emmanuelponsone/Swim_Timing/03 - Electronic Design/altium/Placa madre/Bottom layer.pdf

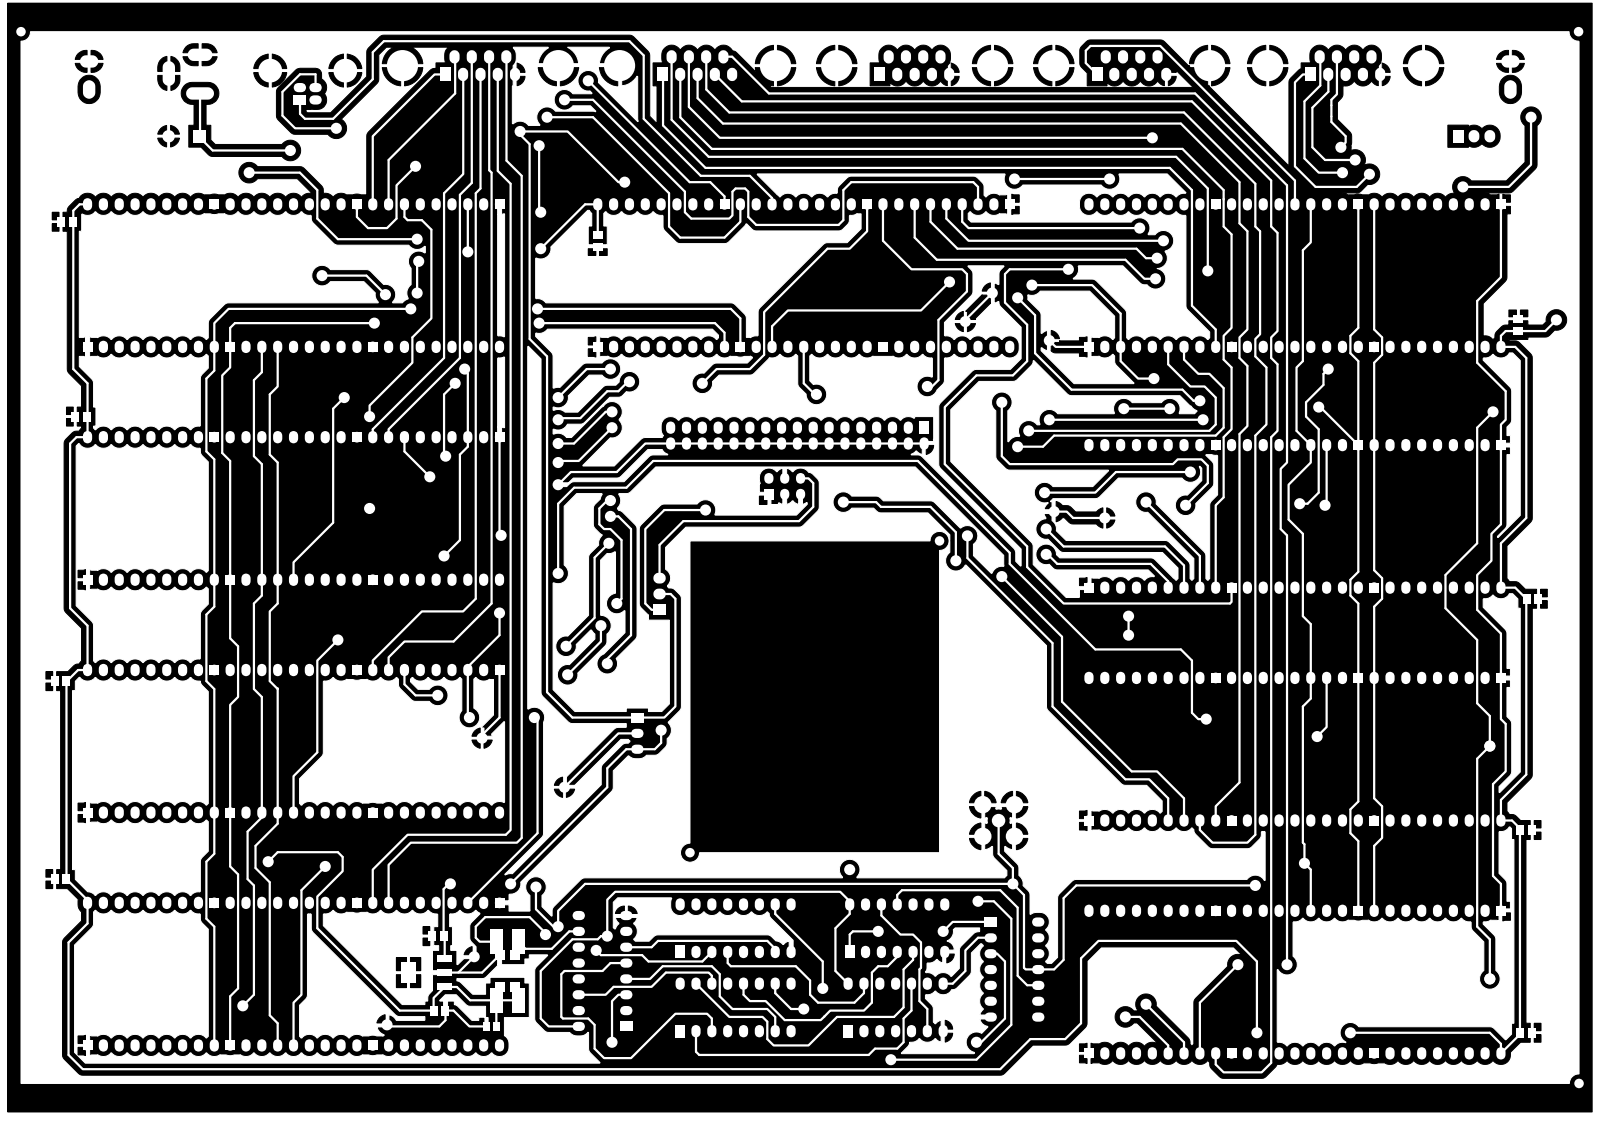
[picture p93: page 1]
