emmanuelponsone/Swim_Timing/03 - Electronic Design/altium/Placa madre/TOP LAYER.pdf

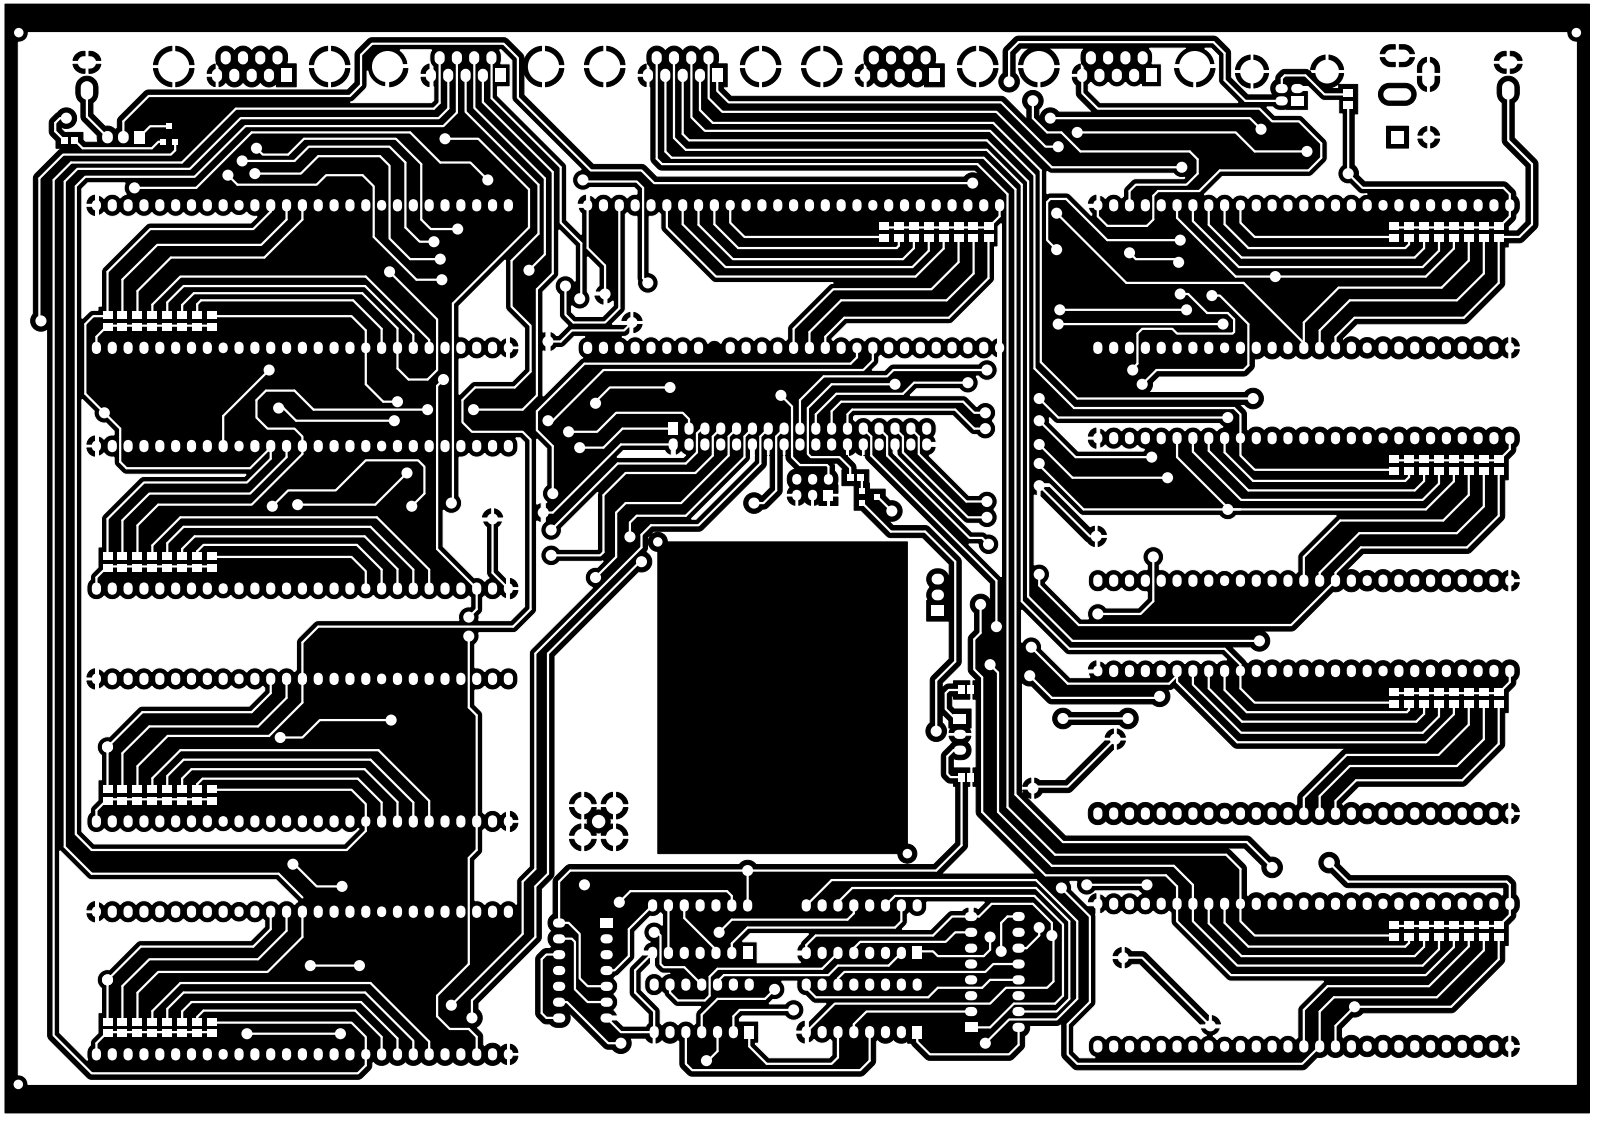
[picture p94: page 1]
