emmanuelponsone/Swim_Timing/03 - Electronic Design/altium/Placa madre 2.0/filminas y nc drill/Bottom layer.pdf

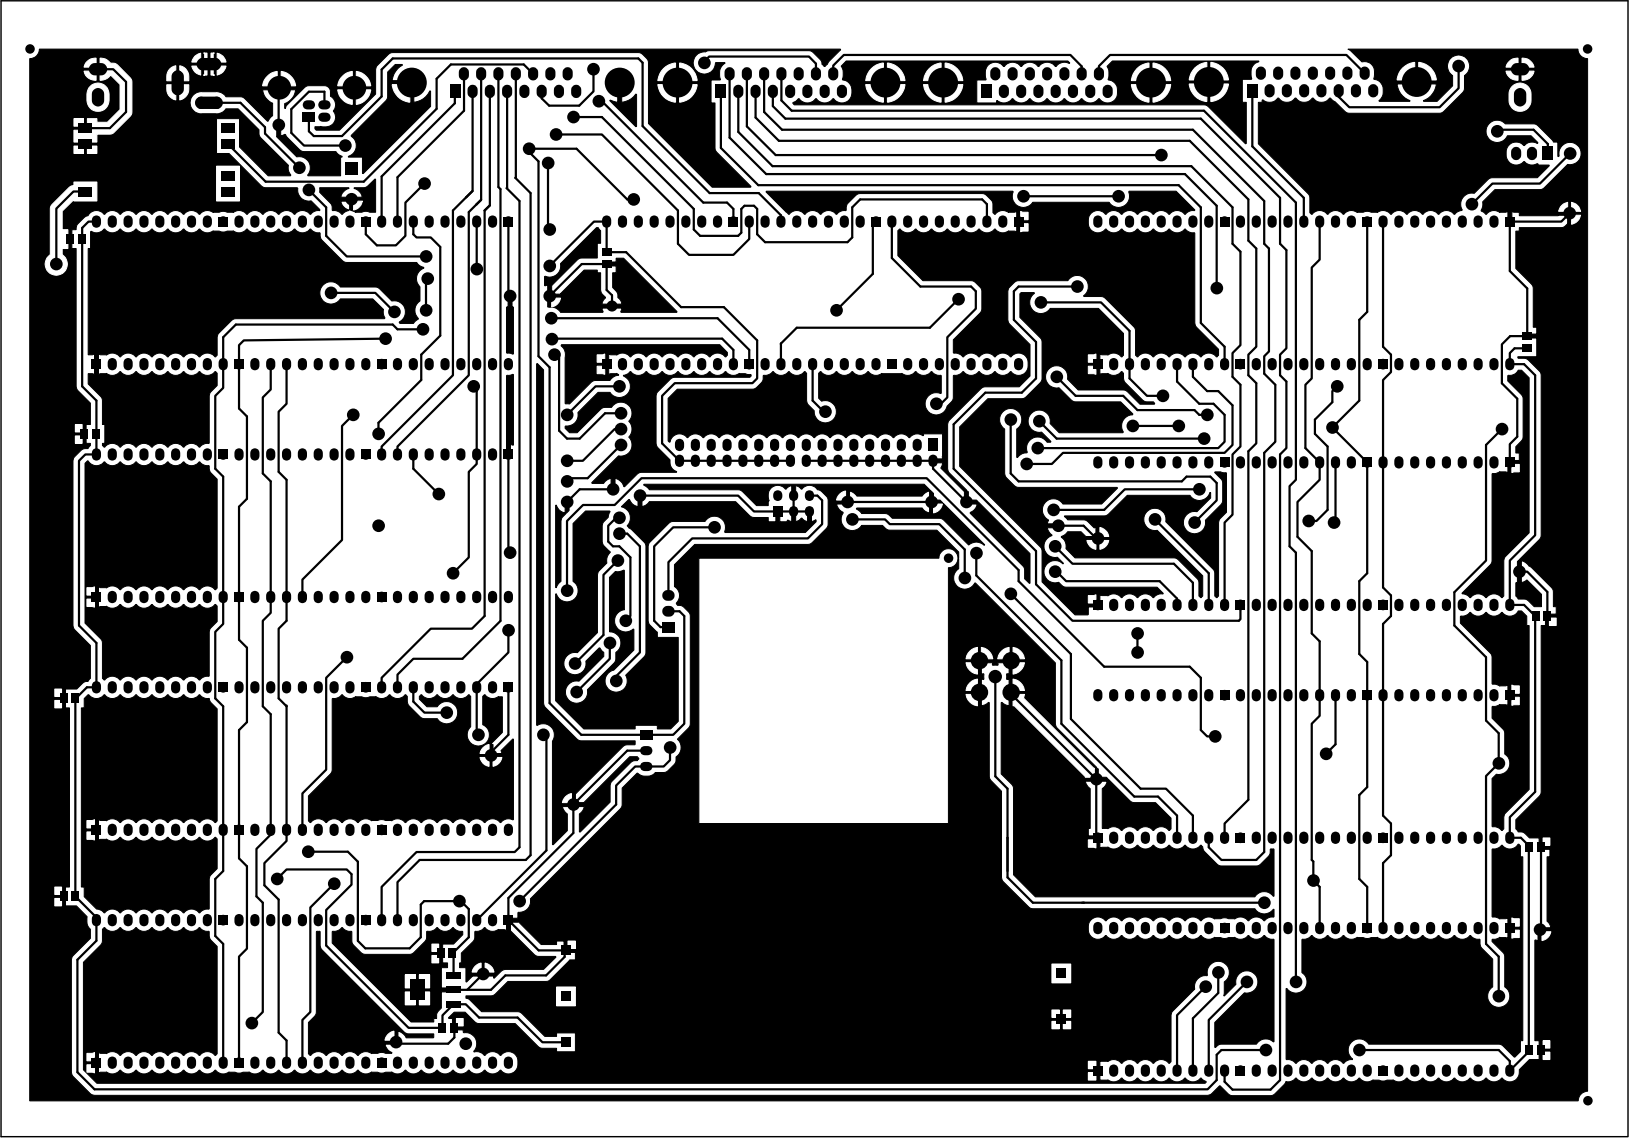
[picture p95: page 1]
