emmanuelponsone/Swim_Timing/03 - Electronic Design/altium/Placa madre 2.0/filminas y nc drill/TOP LAYER.pdf

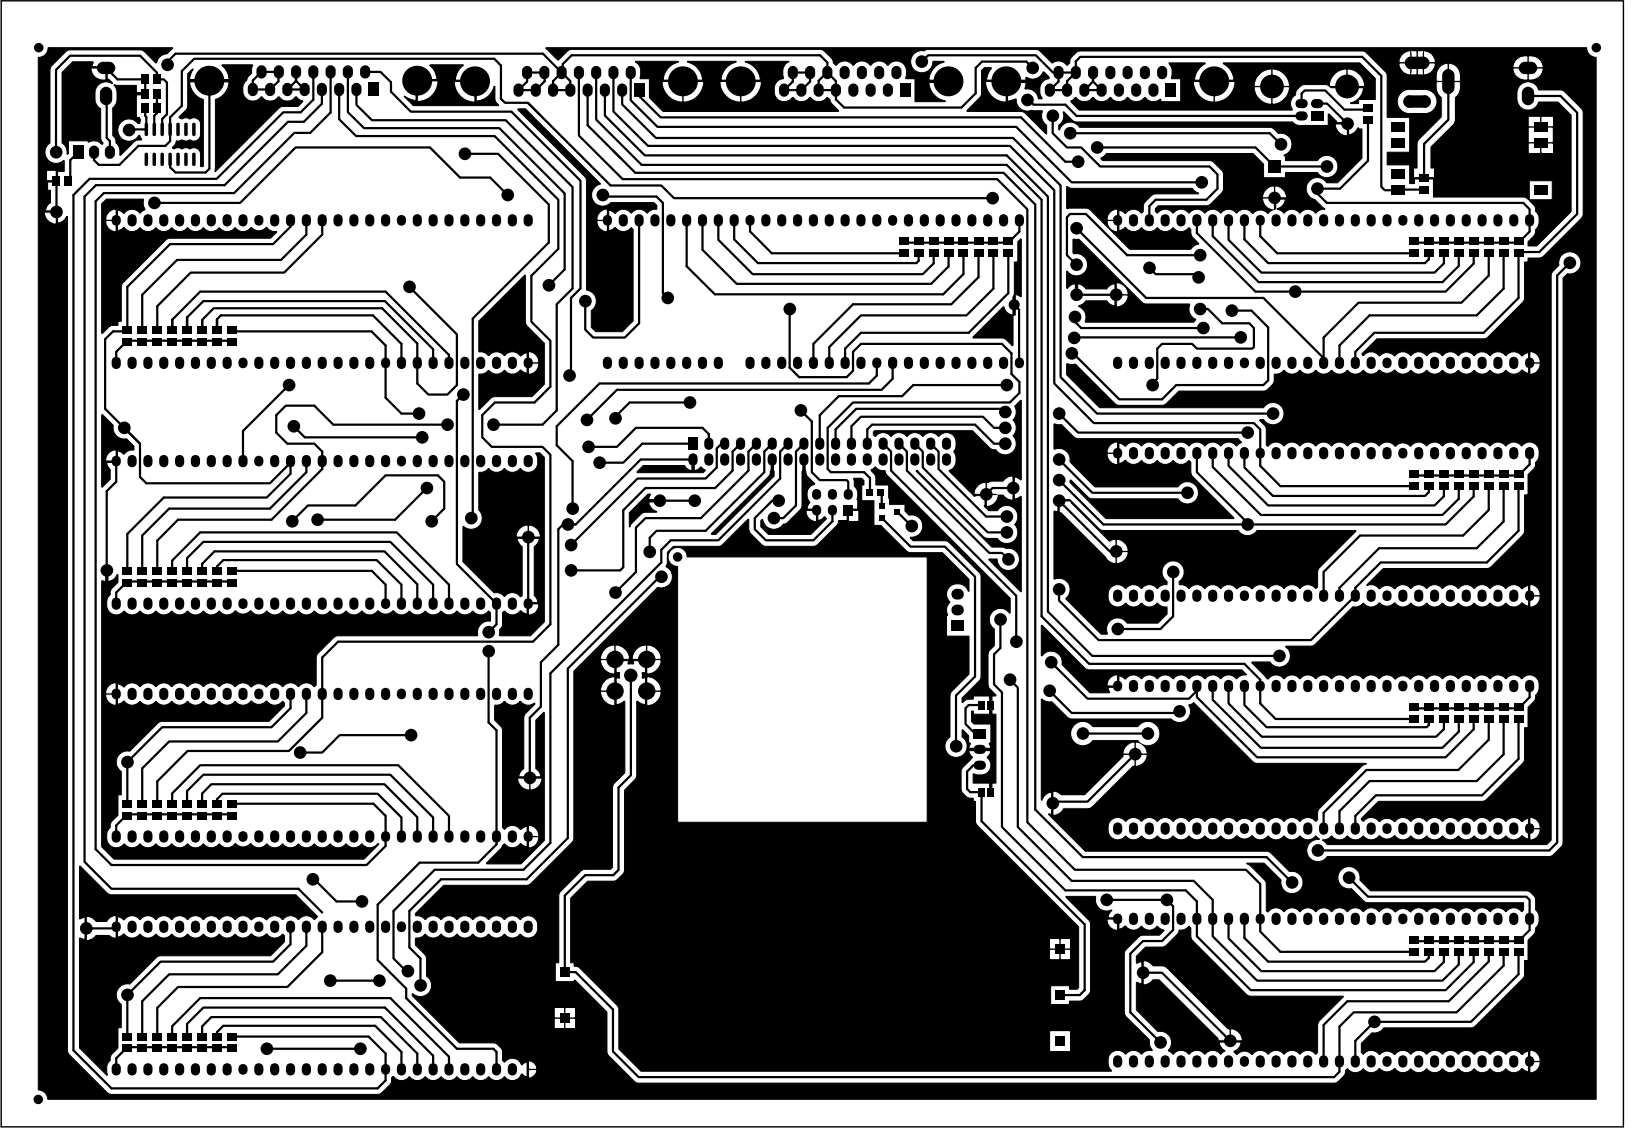
[picture p96: page 1]
