emmanuelponsone/Swim_Timing/03 - Electronic Design/altium/Placa madre/filminas/bottom layer.pdf

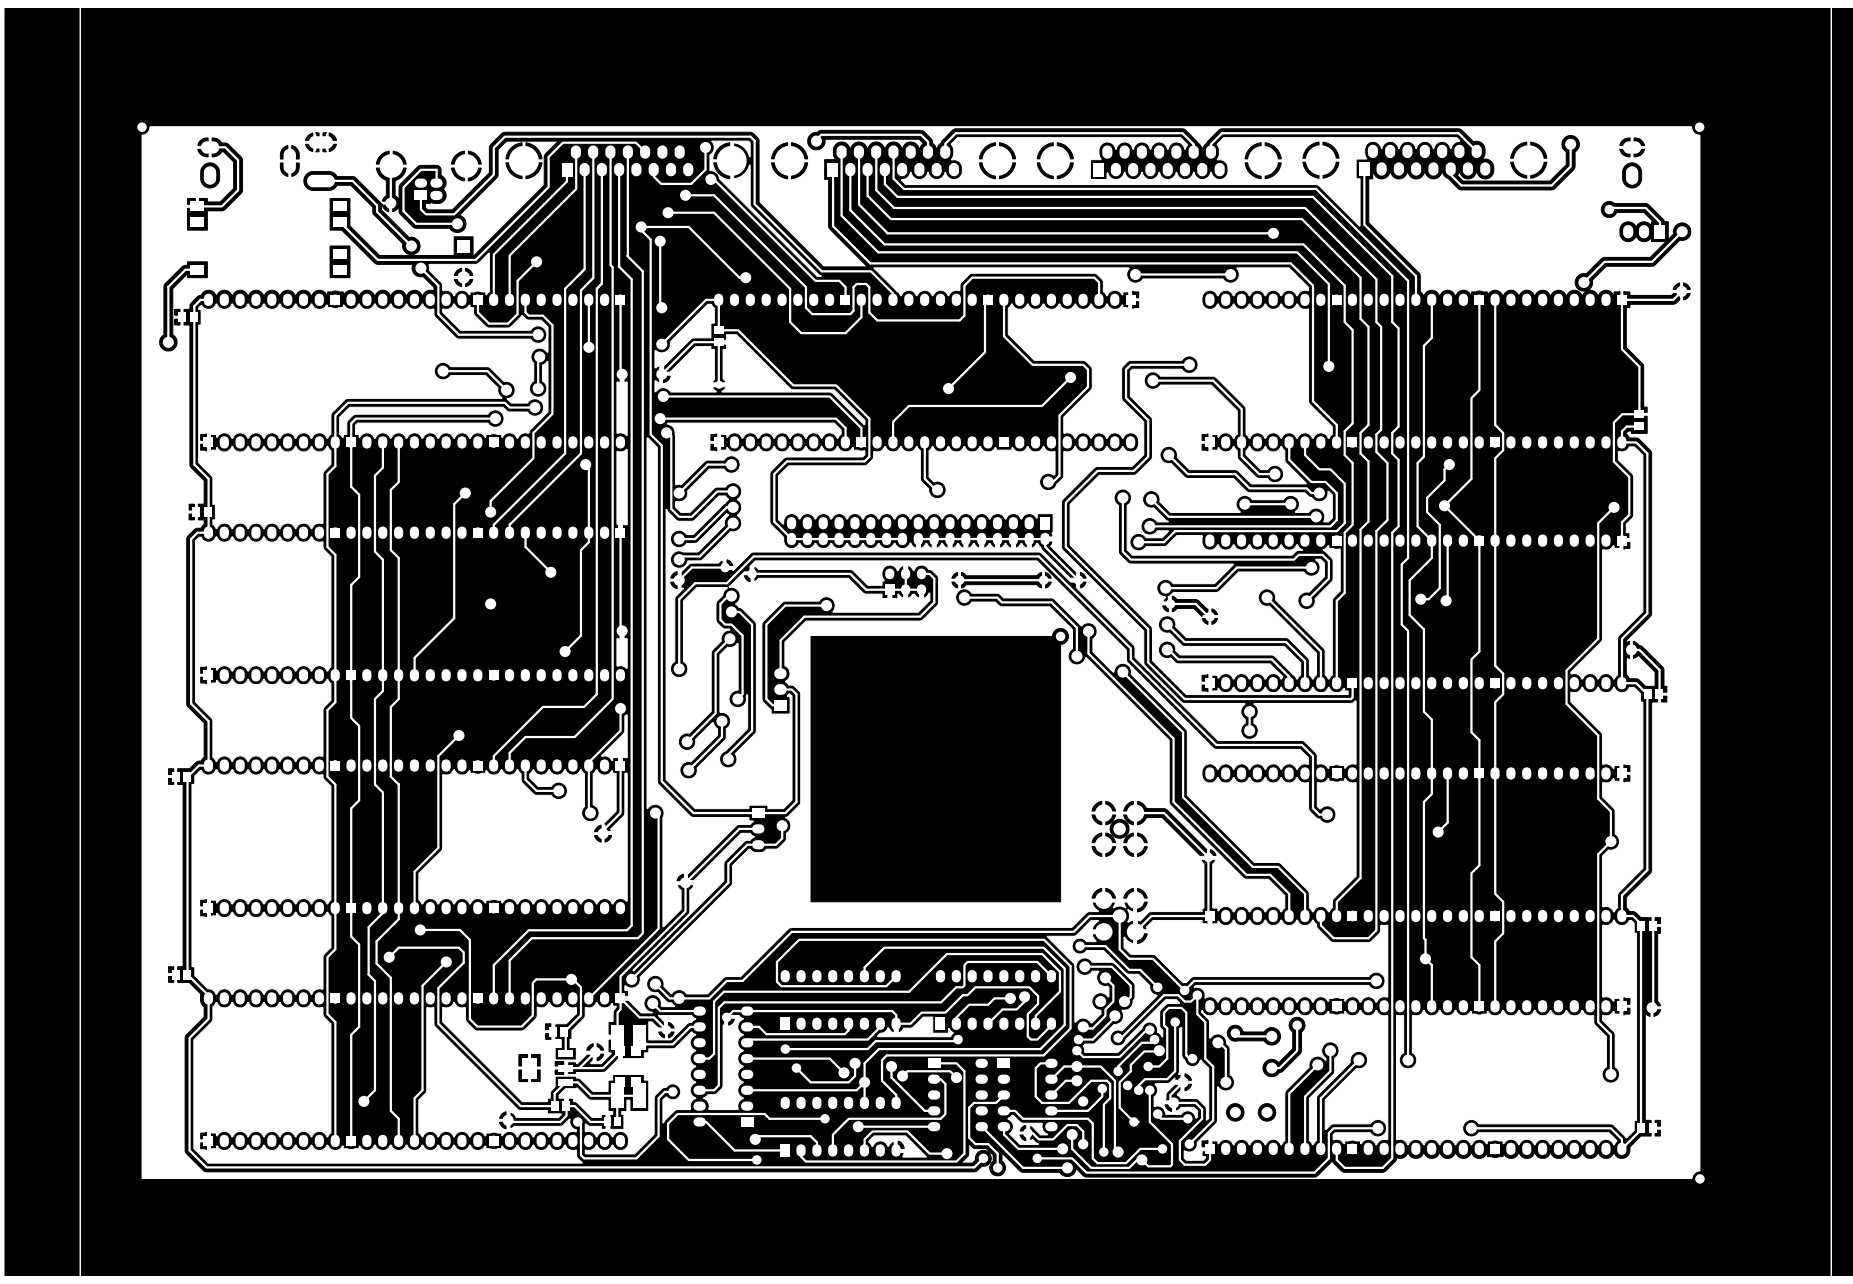
[picture p97: page 1]
