emmanuelponsone/Swim_Timing/03 - Electronic Design/altium/Placa madre/filminas/top layer.pdf

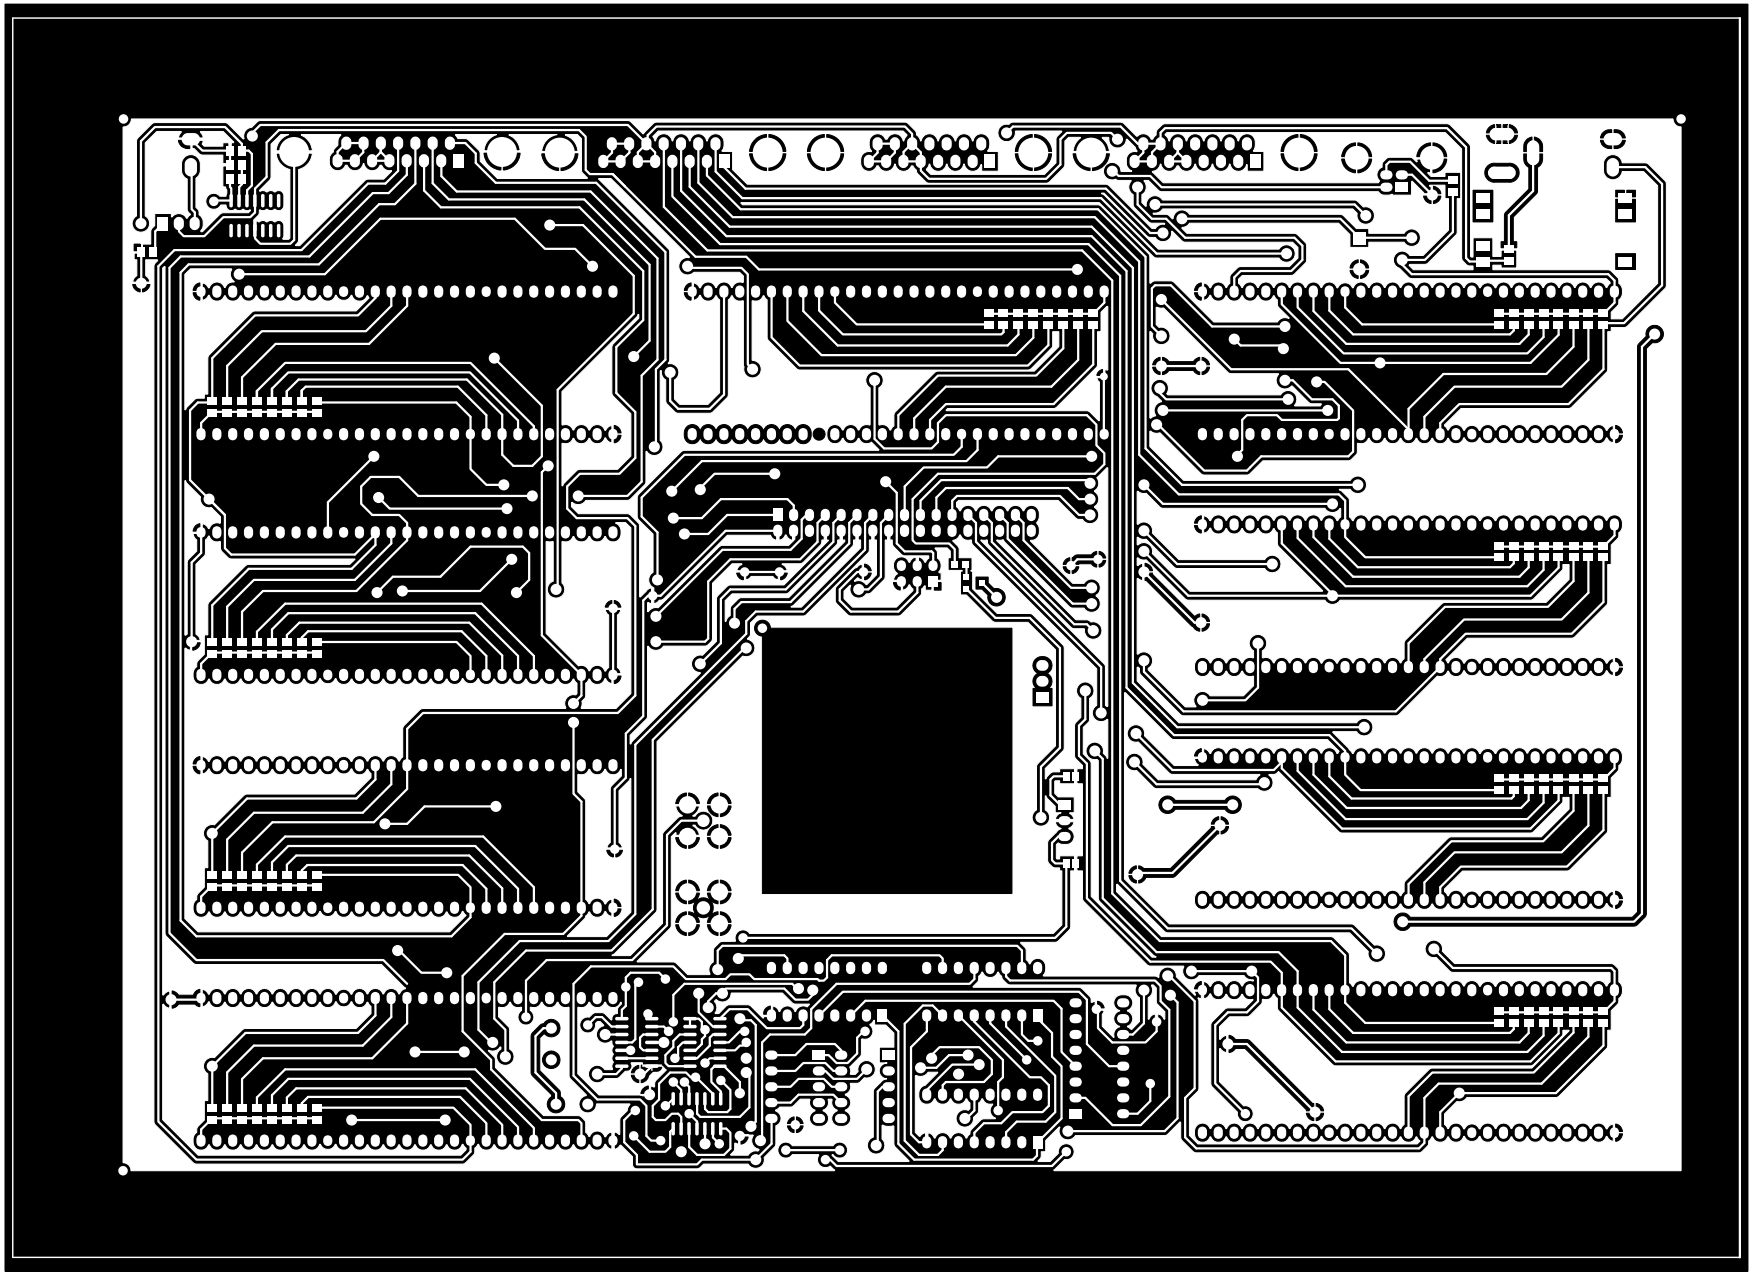
[picture p98: page 1]
