emmanuelponsone/Swim_Timing/03 - Electronic Design/altium/Conexion unidad central/Filminas/adaptador lado unidad central/bottom layer.pdf

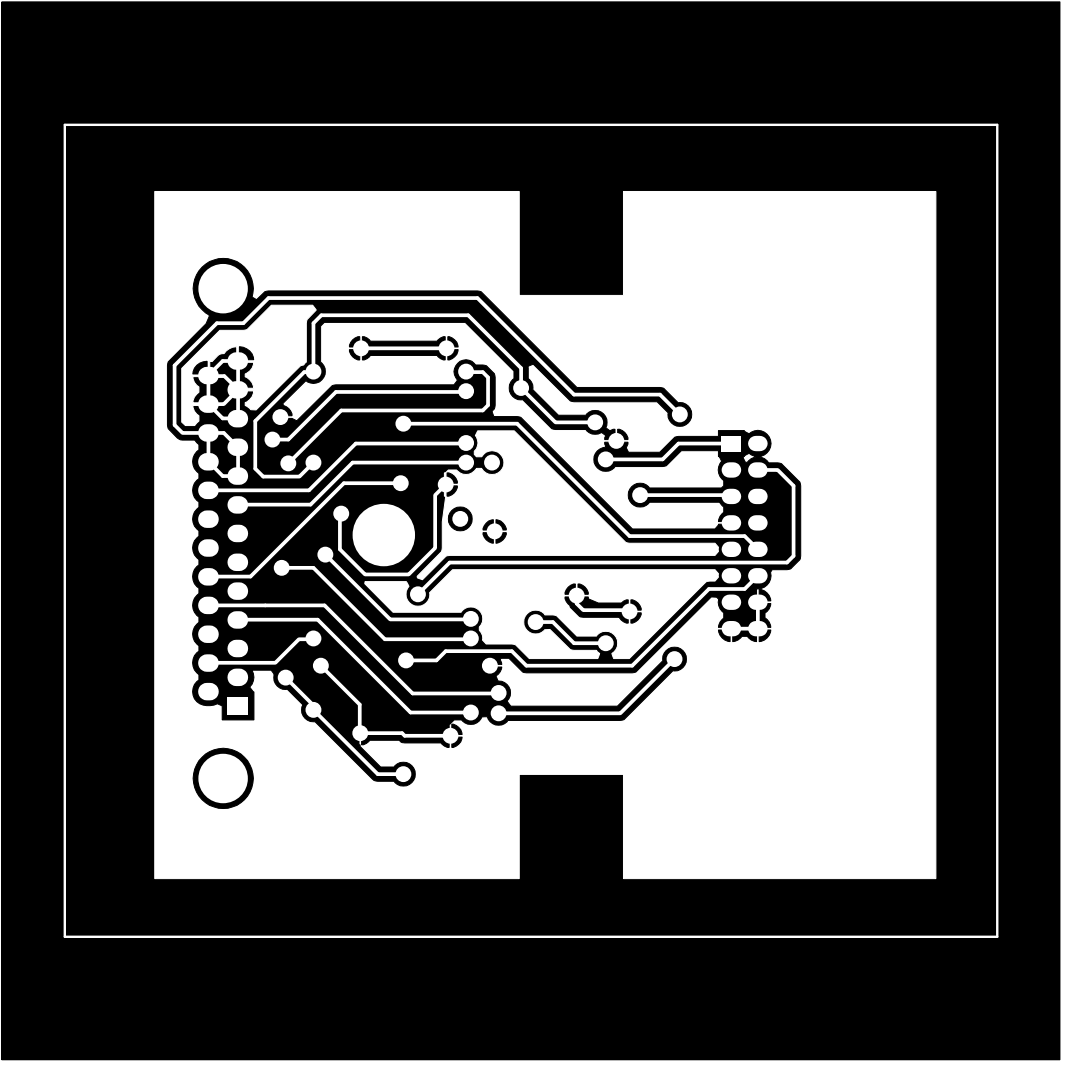
[picture p99: page 1]
