emmanuelponsone/Swim_Timing/03 - Electronic Design/altium/Conexion unidad central/Filminas/adaptador lado unidad central/top layer.pdf

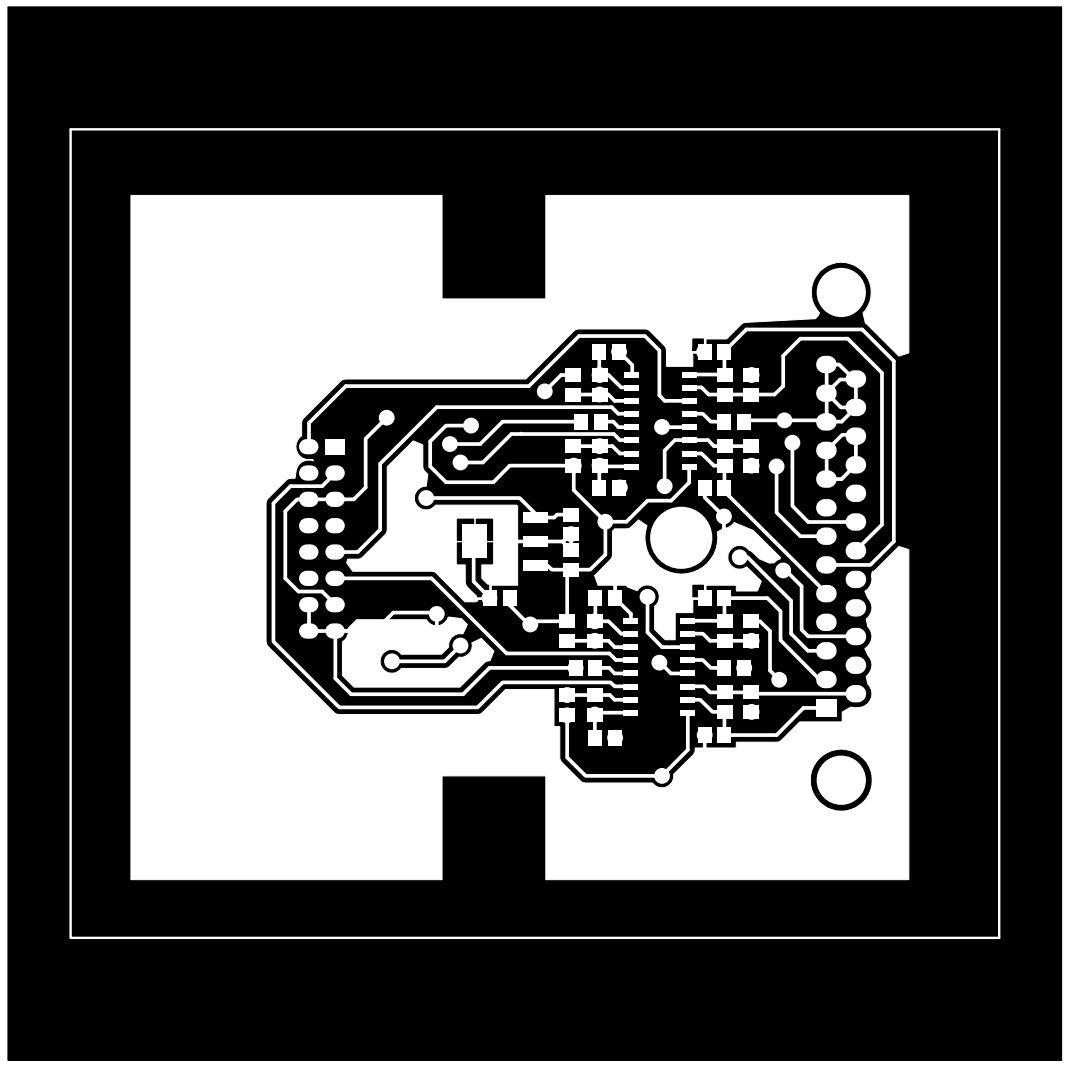
[picture p100: page 1]
