emmanuelponsone/Swim_Timing/03 - Electronic Design/altium/Conexion unidad central/Filminas/caja de conexion/filminas.pdf

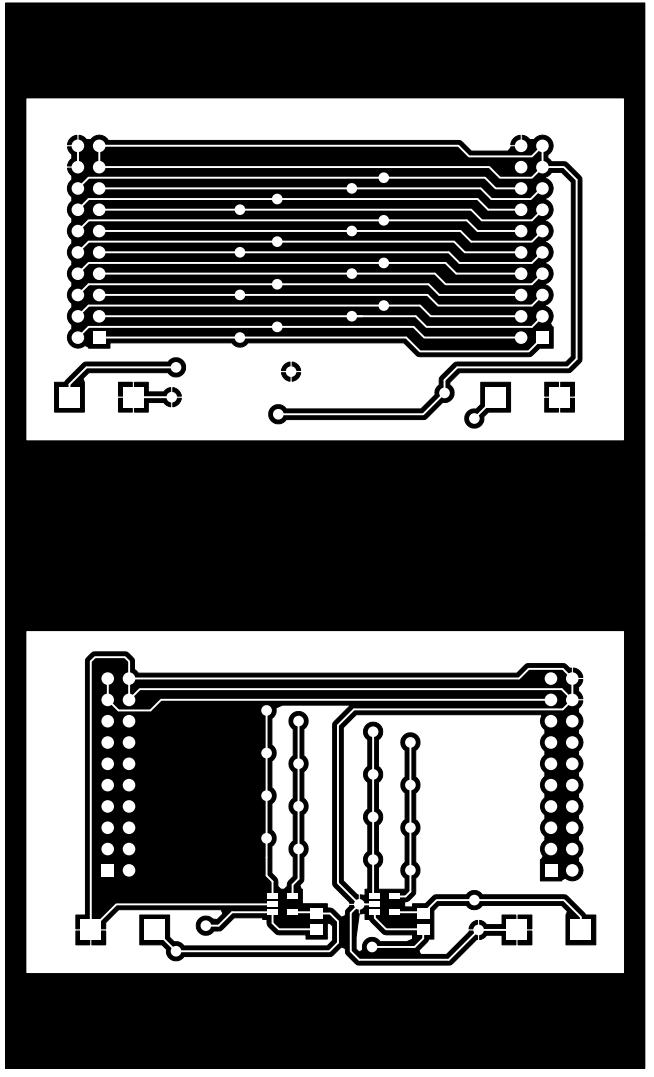
[picture p101: page 1]
