emmanuelponsone/Swim_Timing/mother board.pdf

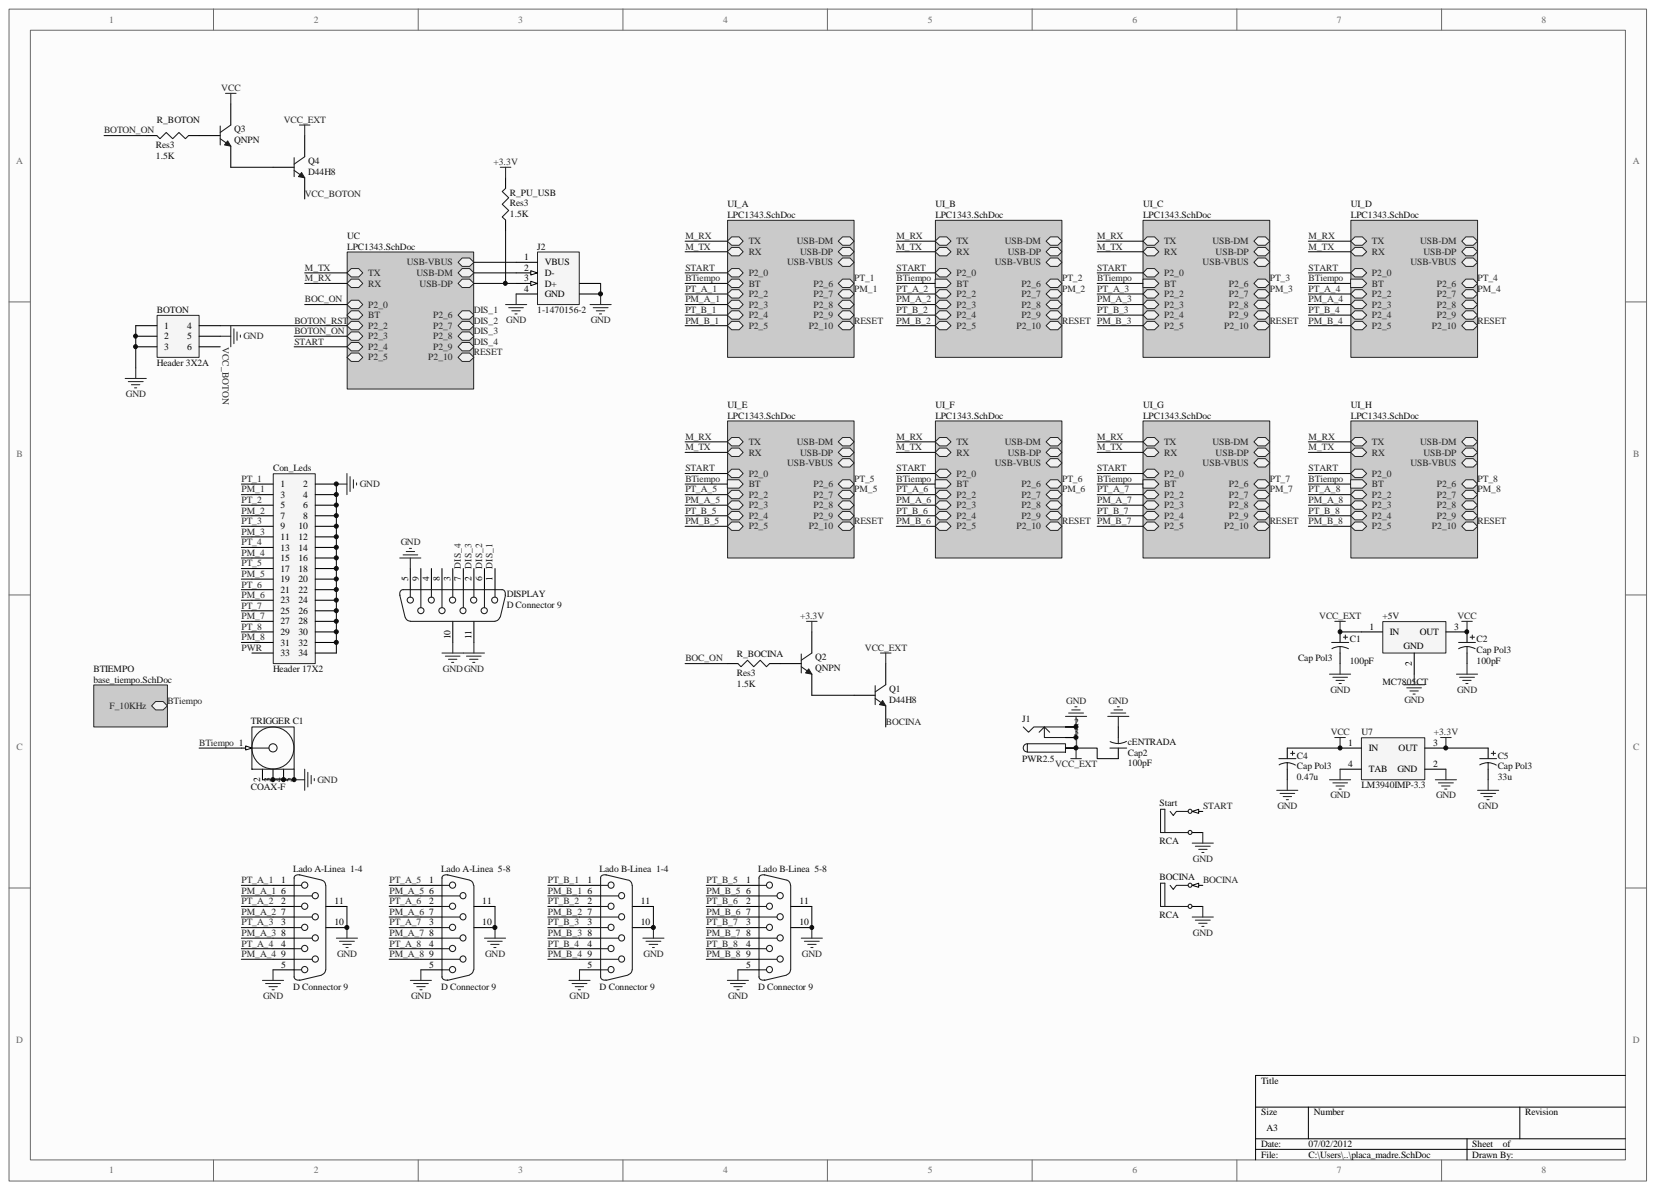
[picture p102: page 1]
