emmanuelponsone/Swim_Timing/01 - Code/00 - Microcontrollers/slaves/src/timer32.c

/*****************************************************************************
 *   timer32.c:  32-bit Timer C file for NXP LPC13xx Family Microprocessors
 *
 *   Copyright(C) 2008, NXP Semiconductor
 *   All rights reserved.
 *
 *   History
 *   2008.08.20  ver 1.00    Preliminary version, first Release
 *
******************************************************************************/
#include "LPC13xx.h"
#include "timer32.h"
#include "gpio.h"
#include "config.h"

#define	ESPERA	10000
#define	ON	 		1
#define	OFF			0
#define A			0
#define B			1
#define MAX_LAPS	50


/* ===================
 * CodeRed - Modified file to extract out interrupt handler related code,
 * which is really application project specific.
 * Set TIMER32_GENERIC_INTS to 1 to reenable original code.
 * =================== */
#ifdef TIMER32_0_DEFAULT_HANDLER
volatile uint32_t timer32_0_counter = 0;
#endif //TIMER32_0_DEFAULT_HANDLER

#ifdef TIMER32_1_DEFAULT_HANDLER
volatile uint32_t timer32_1_counter = 0;
#endif //TIMER32_1_DEFAULT_HANDLER
//extern int TICKS,level;
extern volatile uint32_t cont_laps;
extern volatile uint32_t contador;
extern unsigned int esperar_PT_A,esperar_PT_B,start;
extern volatile uint32_t centesimas,lado,ultimo,lap[MAX_LAPS];




/*****************************************************************************
** Function name:		delay32Ms
**
** Descriptions:		Start the timer delay in milo seconds
**						until elapsed
**
** parameters:			timer number, Delay value in milo second			 
** 						
** Returned value:		None
** 
*****************************************************************************/
void delay32Ms(uint8_t timer_num, uint32_t delayInMs)
{
  if (timer_num == 0)
  {
    /* setup timer #0 for delay */
    LPC_TMR32B0->TCR = 0x02;		/* reset timer */
    LPC_TMR32B0->PR  = 0x00;		/* set prescaler to zero */
    LPC_TMR32B0->MR0 = delayInMs * ((SystemFrequency/LPC_SYSCON->SYSAHBCLKDIV) / 1000);
    LPC_TMR32B0->IR  = 0xff;		/* reset all interrrupts */
    LPC_TMR32B0->MCR = 0x04;		/* stop timer on match */
    LPC_TMR32B0->TCR = 0x01;		/* start timer */
  
    /* wait until delay time has elapsed */
    while (LPC_TMR32B0->TCR & 0x01);
  }
  else if (timer_num == 1)
  {
    /* setup timer #1 for delay */
    LPC_TMR32B1->TCR = 0x02;		/* reset timer */
    LPC_TMR32B1->PR  = 0x00;		/* set prescaler to zero */
    LPC_TMR32B1->MR0 = delayInMs * ((SystemFrequency/LPC_SYSCON->SYSAHBCLKDIV) / 1000);
    LPC_TMR32B1->IR  = 0xff;		/* reset all interrrupts */
    LPC_TMR32B1->MCR = 0x04;		/* stop timer on match */
    LPC_TMR32B1->TCR = 0x01;		/* start timer */
  
    /* wait until delay time has elapsed */
    while (LPC_TMR32B1->TCR & 0x01);
  }
  return;
}


#ifdef TIMER32_0_DEFAULT_HANDLER
/******************************************************************************
** Function name:		TIMER32_0_IRQHandler
**
** Descriptions:		Timer/Counter 0 interrupt handler
**						executes each 10ms @ 60 MHz CPU Clock
**
** parameters:			None
** Returned value:		None
** 
******************************************************************************/
void TIMER32_0_IRQHandler(void)
{  
LPC_TMR32B0->IR = 1;			/* clear interrupt flag */
timer32_0_counter++;
start=ON;
if(start==ON)
{
	centesimas++;
}
if(esperar_PT_A==ON)
{
	contador++;
	if(contador==ESPERA)	//Se cumplio el tiempo de espera. Se utiliza el tiempo de la PM
	{
		contador=0;		//Reseteo el contador
		esperar_PT_A=OFF;	//Bajo el flag de espera
		ultimo=lap[cont_laps];
		cont_laps++;	//Aumento el numero de laps
		lado=B;
		GPIOIntDisable( PORT2, 2 );	//Dehabilito las interrupciones de la PT_A
		GPIOIntClear( PORT2, 4 );
		GPIOIntClear( PORT2, 5 );
		GPIOIntEnable( PORT2, 4 );	//Habilita las interrupciones de los pulsadores del otro lado de la pileta
		GPIOIntEnable( PORT2, 5 );
	}
}
if(esperar_PT_B==ON)
{
	contador++;
	if(contador==ESPERA)	//Se cumplio el tiempo de espera. Se utiliza el tiempo de la PM
	{
		contador=0;		//Reseteo el contador
		esperar_PT_B=OFF;	//Bajo el flag de espera
		ultimo=lap[cont_laps];
		cont_laps++;	//Aumento el numero de laps
		lado=A;
		GPIOIntDisable( PORT2, 4 );	//Dehabilito las interrupciones de la PT_B
		GPIOIntClear( PORT2, 2 );
		GPIOIntClear( PORT2, 3 );
		GPIOIntEnable( PORT2, 2 );	//Habilita las interrupciones de los pulsadores del otro lado de la pileta
		GPIOIntEnable( PORT2, 3 );

	}
}

return;
}
#endif //TIMER32_0_DEFAULT_HANDLER

#ifdef TIMER32_1_DEFAULT_HANDLER
/******************************************************************************
** Function name:		TIMER32_1_IRQHandler
**
** Descriptions:		Timer/Counter 1 interrupt handler
**						executes each 10ms @ 60 MHz CPU Clock
**
** parameters:			None
** Returned value:		None
** 
******************************************************************************/
void TIMER32_1_IRQHandler(void)
{  
  LPC_TMR32B1->IR = 1;			/* clear interrupt flag */
  timer32_1_counter++;
  return;
}
#endif //TIMER32_1_DEFAULT_HANDLER

/******************************************************************************
** Function name:		enable_timer
**
** Descriptions:		Enable timer
**
** parameters:			timer number: 0 or 1
** Returned value:		None
** 
******************************************************************************/
void enable_timer32(uint8_t timer_num)
{
  if ( timer_num == 0 )
  {
    LPC_TMR32B0->TCR = 1;
  }
  else
  {
    LPC_TMR32B1->TCR = 1;
  }
  return;
}

/******************************************************************************
** Function name:		disable_timer
**
** Descriptions:		Disable timer
**
** parameters:			timer number: 0 or 1
** Returned value:		None
** 
******************************************************************************/
void disable_timer32(uint8_t timer_num)
{
  if ( timer_num == 0 )
  {
    LPC_TMR32B0->TCR = 0;
  }
  else
  {
    LPC_TMR32B1->TCR = 0;
  }
  return;
}

/******************************************************************************
** Function name:		reset_timer
**
** Descriptions:		Reset timer
**
** parameters:			timer number: 0 or 1
** Returned value:		None
** 
******************************************************************************/
void reset_timer32(uint8_t timer_num)
{
  uint32_t regVal;

  if ( timer_num == 0 )
  {
    regVal = LPC_TMR32B0->TCR;
    regVal |= 0x02;
    LPC_TMR32B0->TCR = regVal;
  }
  else
  {
    regVal = LPC_TMR32B1->TCR;
    regVal |= 0x02;
    LPC_TMR32B1->TCR = regVal;
  }
  return;
}

/******************************************************************************
** Function name:		init_timer
**
** Descriptions:		Initialize timer, set timer interval, reset timer,
**						install timer interrupt handler
**
** parameters:			timer number and timer interval
** Returned value:		None
** 
******************************************************************************/
void init_timer32(uint8_t timer_num, uint32_t TimerInterval) 
{
  if ( timer_num == 0 )
  {
    /* Some of the I/O pins need to be carefully planned if
    you use below module because JTAG and TIMER CAP/MAT pins are muxed. */
    LPC_SYSCON->SYSAHBCLKCTRL |= (1<<9);
    LPC_IOCON->PIO1_5 &= ~0x07;	/*  Timer0_32 I/O config */
    LPC_IOCON->PIO1_5 |= 0x02;	/* Timer0_32 CAP0 */
    LPC_IOCON->PIO1_6 &= ~0x07;
    LPC_IOCON->PIO1_6 |= 0x02;	/* Timer0_32 MAT0 */
    LPC_IOCON->PIO1_7 &= ~0x07;
    LPC_IOCON->PIO1_7 |= 0x02;	/* Timer0_32 MAT1 */
    LPC_IOCON->PIO0_1 &= ~0x07;	
    LPC_IOCON->PIO0_1 |= 0x02;	/* Timer0_32 MAT2 */
#ifdef __JTAG_DISABLED
    LPC_IOCON->JTAG_TDI_PIO0_11 &= ~0x07;	
    LPC_IOCON->JTAG_TDI_PIO0_11 |= 0x03;	/* Timer0_32 MAT3 */
#endif
#ifdef TIMER32_0_DEFAULT_HANDLER
    timer32_0_counter = 0;
#endif //TIMER32_0_DEFAULT_HANDLER
    LPC_TMR32B0->MR0 = TimerInterval;
//	LPC_TMR32B0->EMR &= ~(0xFF<<4);
//	LPC_TMR32B0->EMR |= (0x03<<4);	/* MR0 Toggle */
    LPC_TMR32B0->MCR = 3;			/* Interrupt and Reset on MR0 */

    /* Enable the TIMER0 Interrupt */
    NVIC_EnableIRQ(TIMER_32_0_IRQn);
  }
  else if ( timer_num == 1 )
  {
    /* Some of the I/O pins need to be clearfully planned if
    you use below module because JTAG and TIMER CAP/MAT pins are muxed. */
    LPC_SYSCON->SYSAHBCLKCTRL |= (1<<10);
#ifdef __JTAG_DISABLED
    LPC_IOCON->JTAG_TMS_PIO1_0  &= ~0x07;	/*  Timer1_32 I/O config */
    LPC_IOCON->JTAG_TMS_PIO1_0  |= 0x03;	/* Timer1_32 CAP0 */
    LPC_IOCON->JTAG_TDO_PIO1_1  &= ~0x07;	
    LPC_IOCON->JTAG_TDO_PIO1_1  |= 0x03;	/* Timer1_32 MAT0 */
    LPC_IOCON->JTAG_nTRST_PIO1_2 &= ~0x07;
    LPC_IOCON->JTAG_nTRST_PIO1_2 |= 0x03;	/* Timer1_32 MAT1 */
    LPC_IOCON->ARM_SWDIO_PIO1_3  &= ~0x07;
    LPC_IOCON->ARM_SWDIO_PIO1_3  |= 0x03;	/* Timer1_32 MAT2 */
#endif
    LPC_IOCON->PIO1_4 &= ~0x07;
    LPC_IOCON->PIO1_4 |= 0x02;		/* Timer0_32 MAT3 */

#ifdef TIMER32_1_DEFAULT_HANDLER
    timer32_1_counter = 0;
#endif //TIMER32_1_DEFAULT_HANDLER

    LPC_TMR32B1->MR0 = TimerInterval;
//	LPC_TMR32B1->EMR &= ~(0xFF<<4);
//	LPC_TMR32B1->EMR |= (0x03<<10);	/* MR3 Toggle */
    LPC_TMR32B1->MCR = 3;			/* Interrupt and Reset on MR0 */

    /* Enable the TIMER1 Interrupt */
    NVIC_EnableIRQ(TIMER_32_1_IRQn);
  }
  return;
}

/******************************************************************************
**                            End Of File
******************************************************************************/
